dumtux/CM4-NAS-MiniPCIE/PICS/JLCPCB Impedance 90R.png

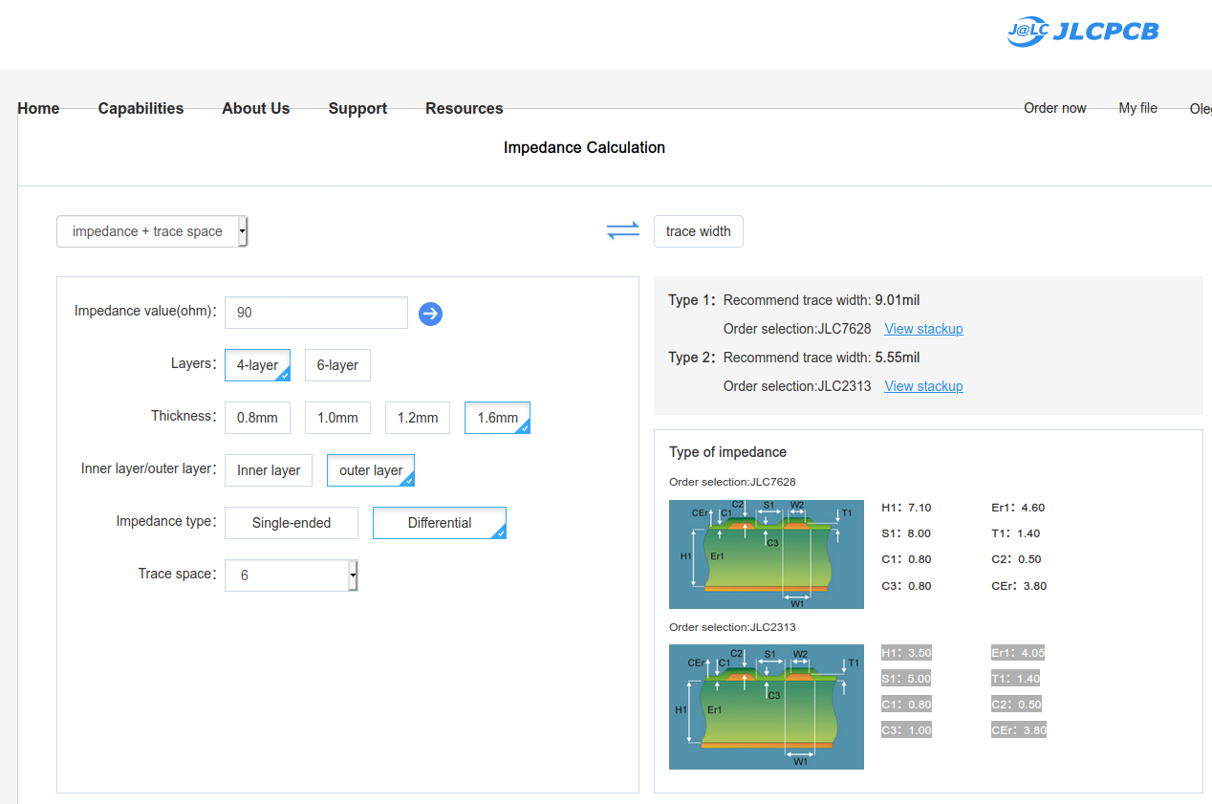
PICS/JLCPCB Impedance 90R.png
